henryvo2k4/RODA/images/IMG20260704133315.jpg

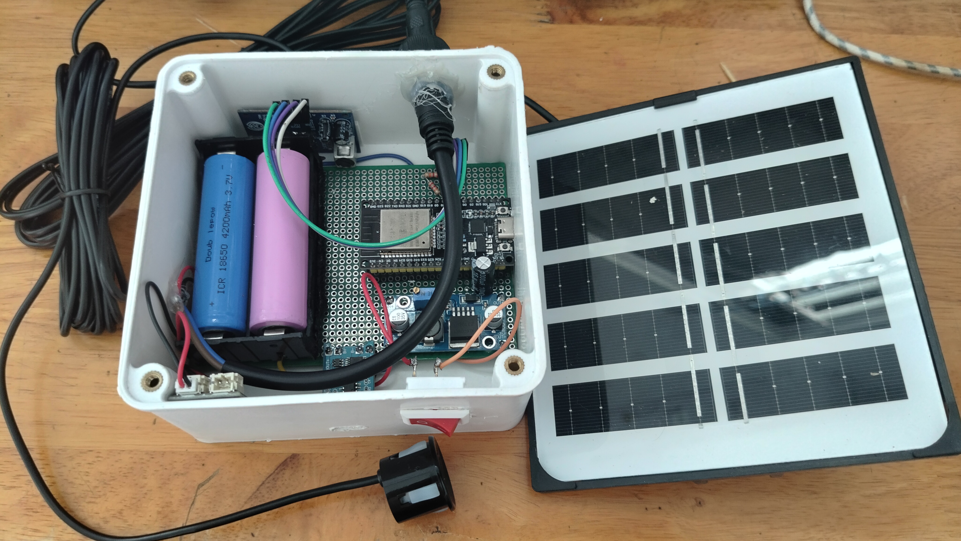
images/IMG20260704133315.jpg
