henryvo2k4/RODA/images/IMG20260704133330.jpg

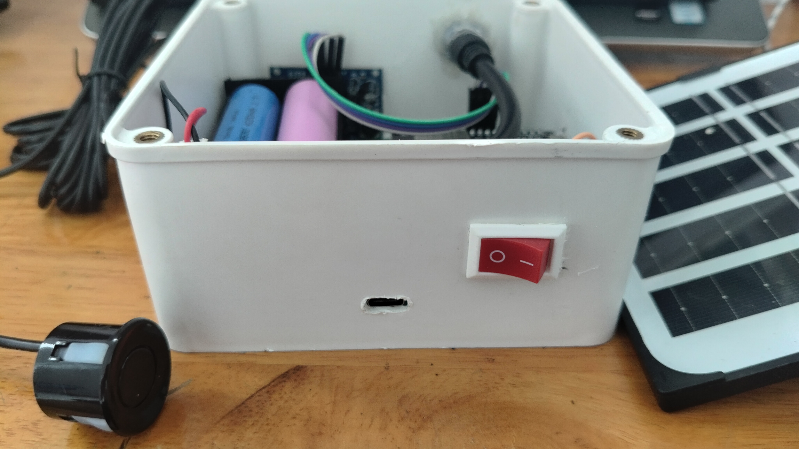
images/IMG20260704133330.jpg
