henryvo2k4/RODA/images/IMG20260704133344.jpg

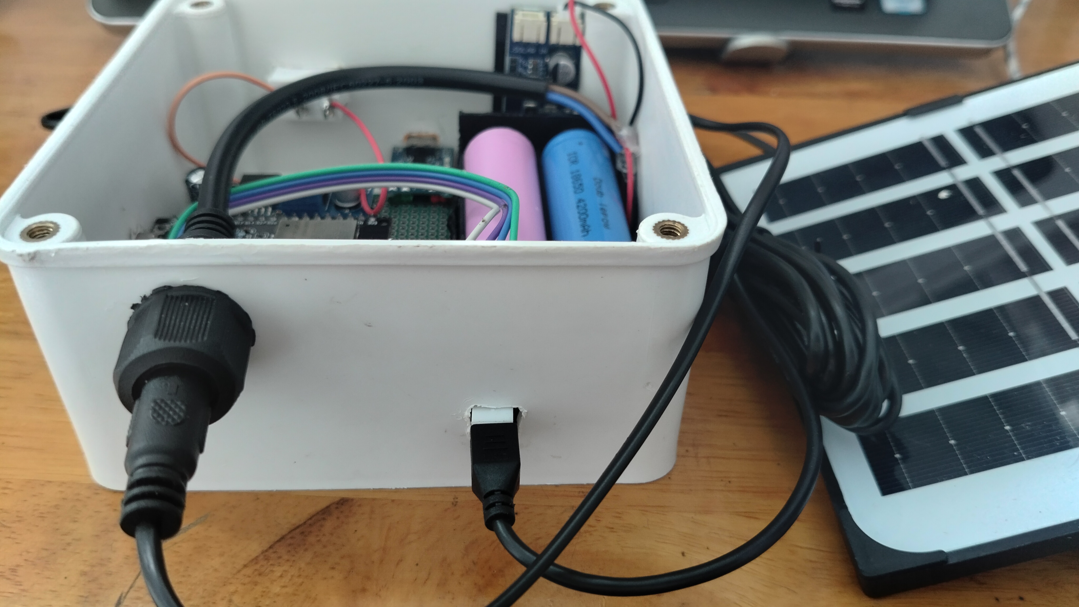
images/IMG20260704133344.jpg
