henryvo2k4/RODA/images/IMG20260704133718.jpg

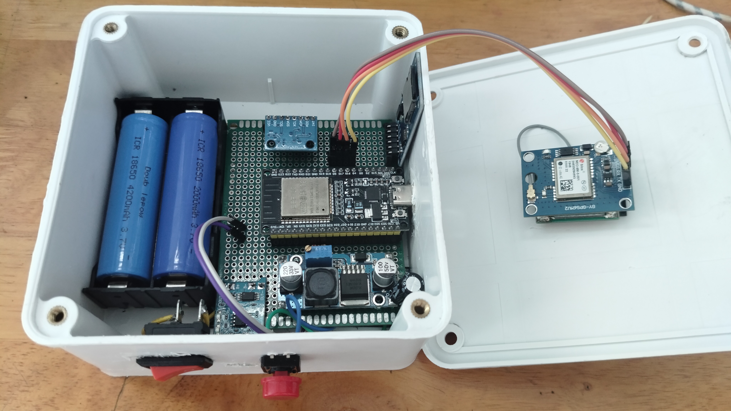
images/IMG20260704133718.jpg
